RunTheBot/NotAHackPad/pcb/hack_pad.kicad_sch

## KiCad design pcb/hack_pad.kicad_sch (2025-06-08)

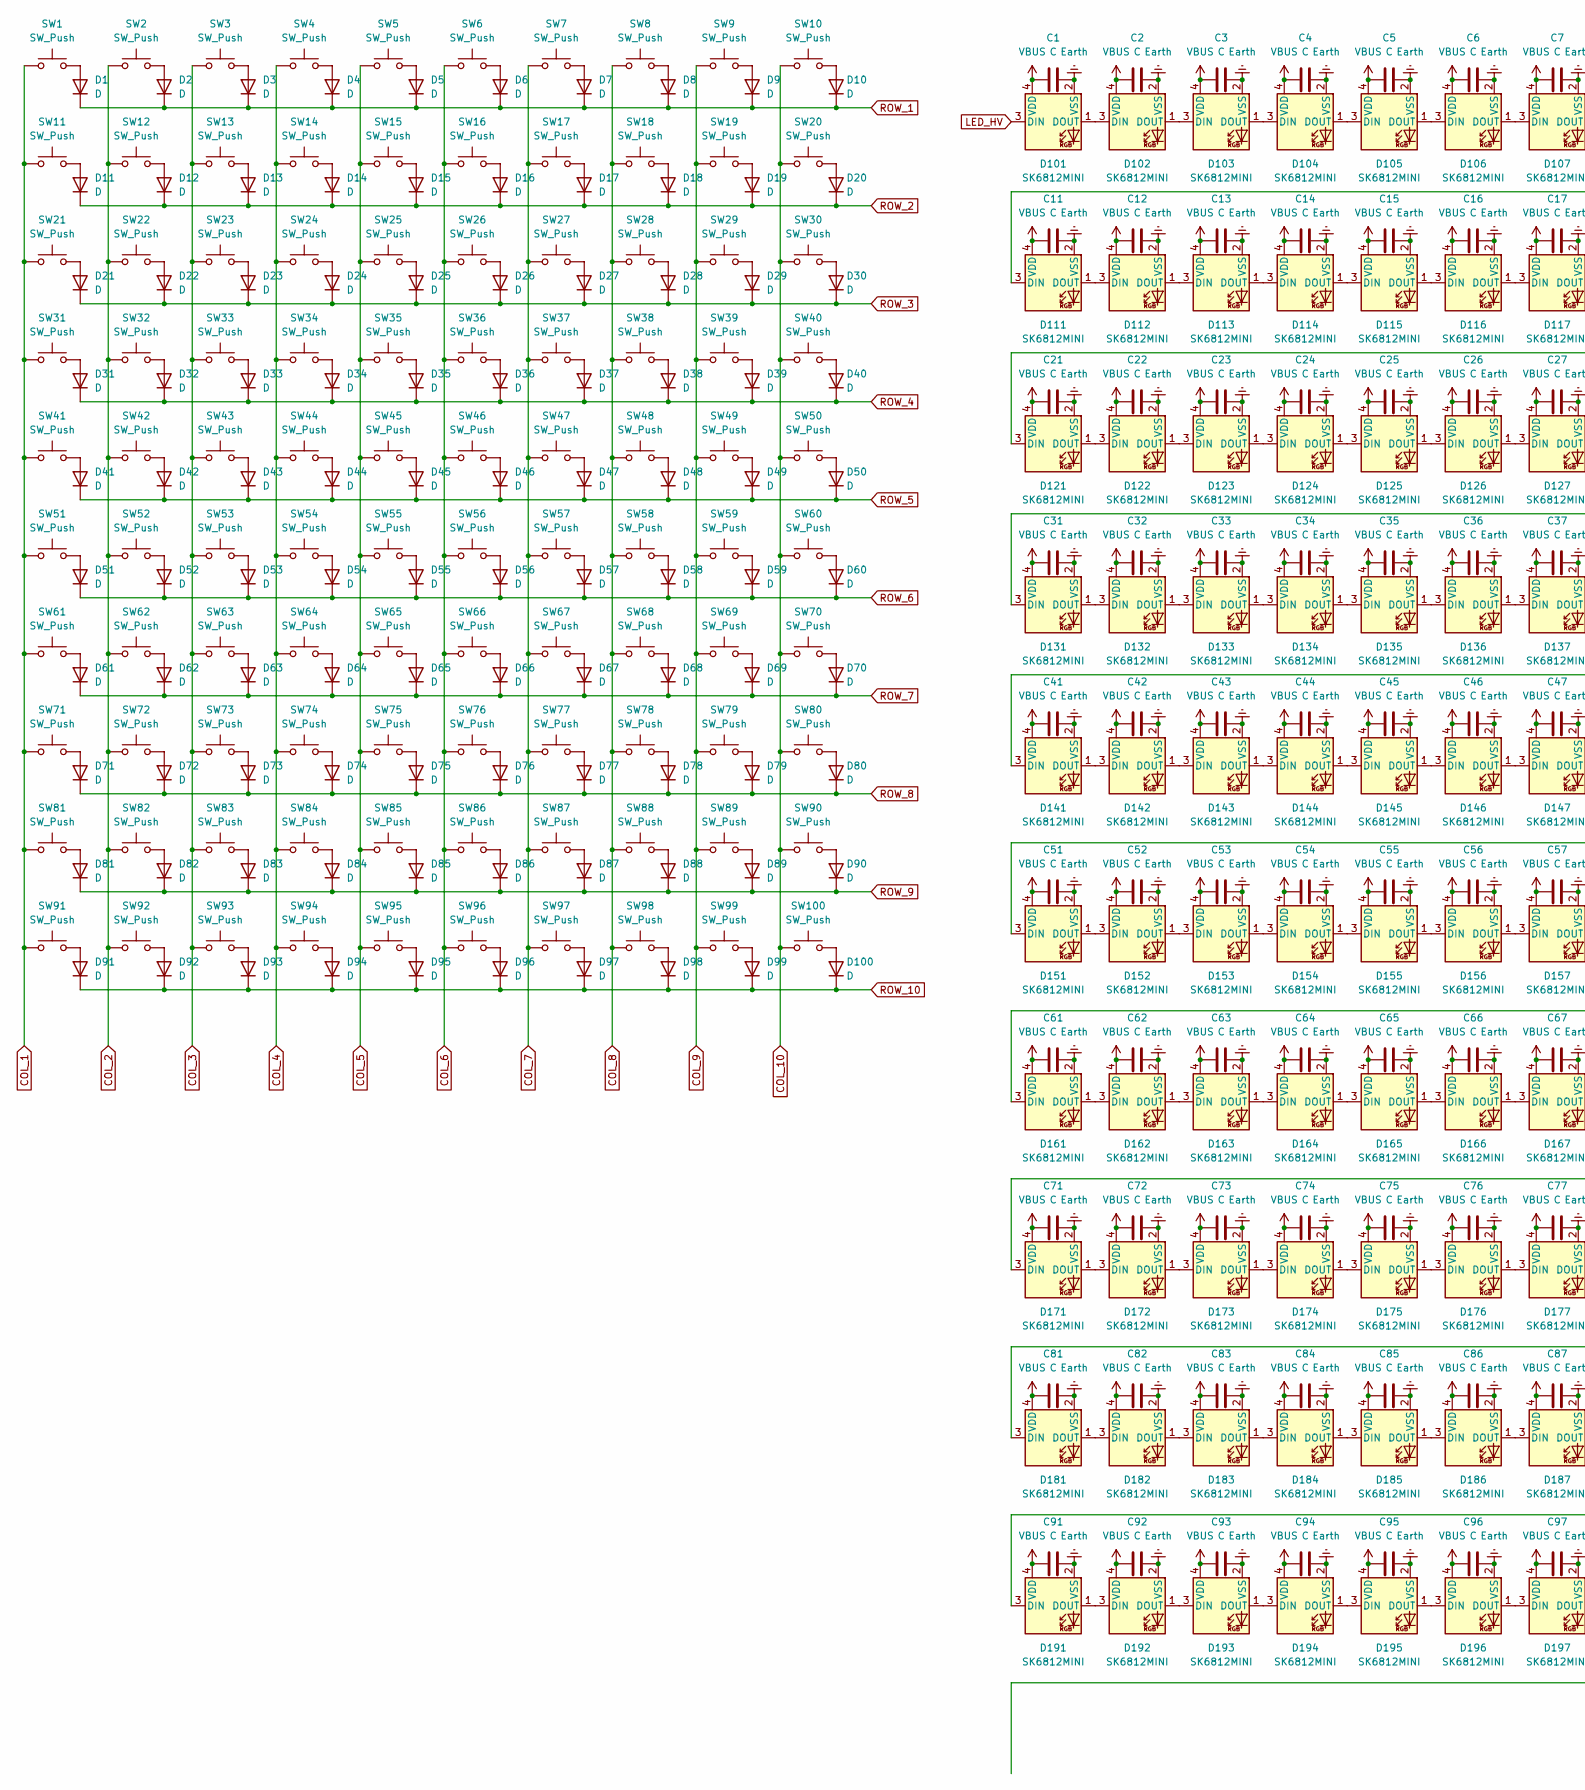
[picture p5: schematic hack_pad.kicad_sch, part in row 1, column 1]

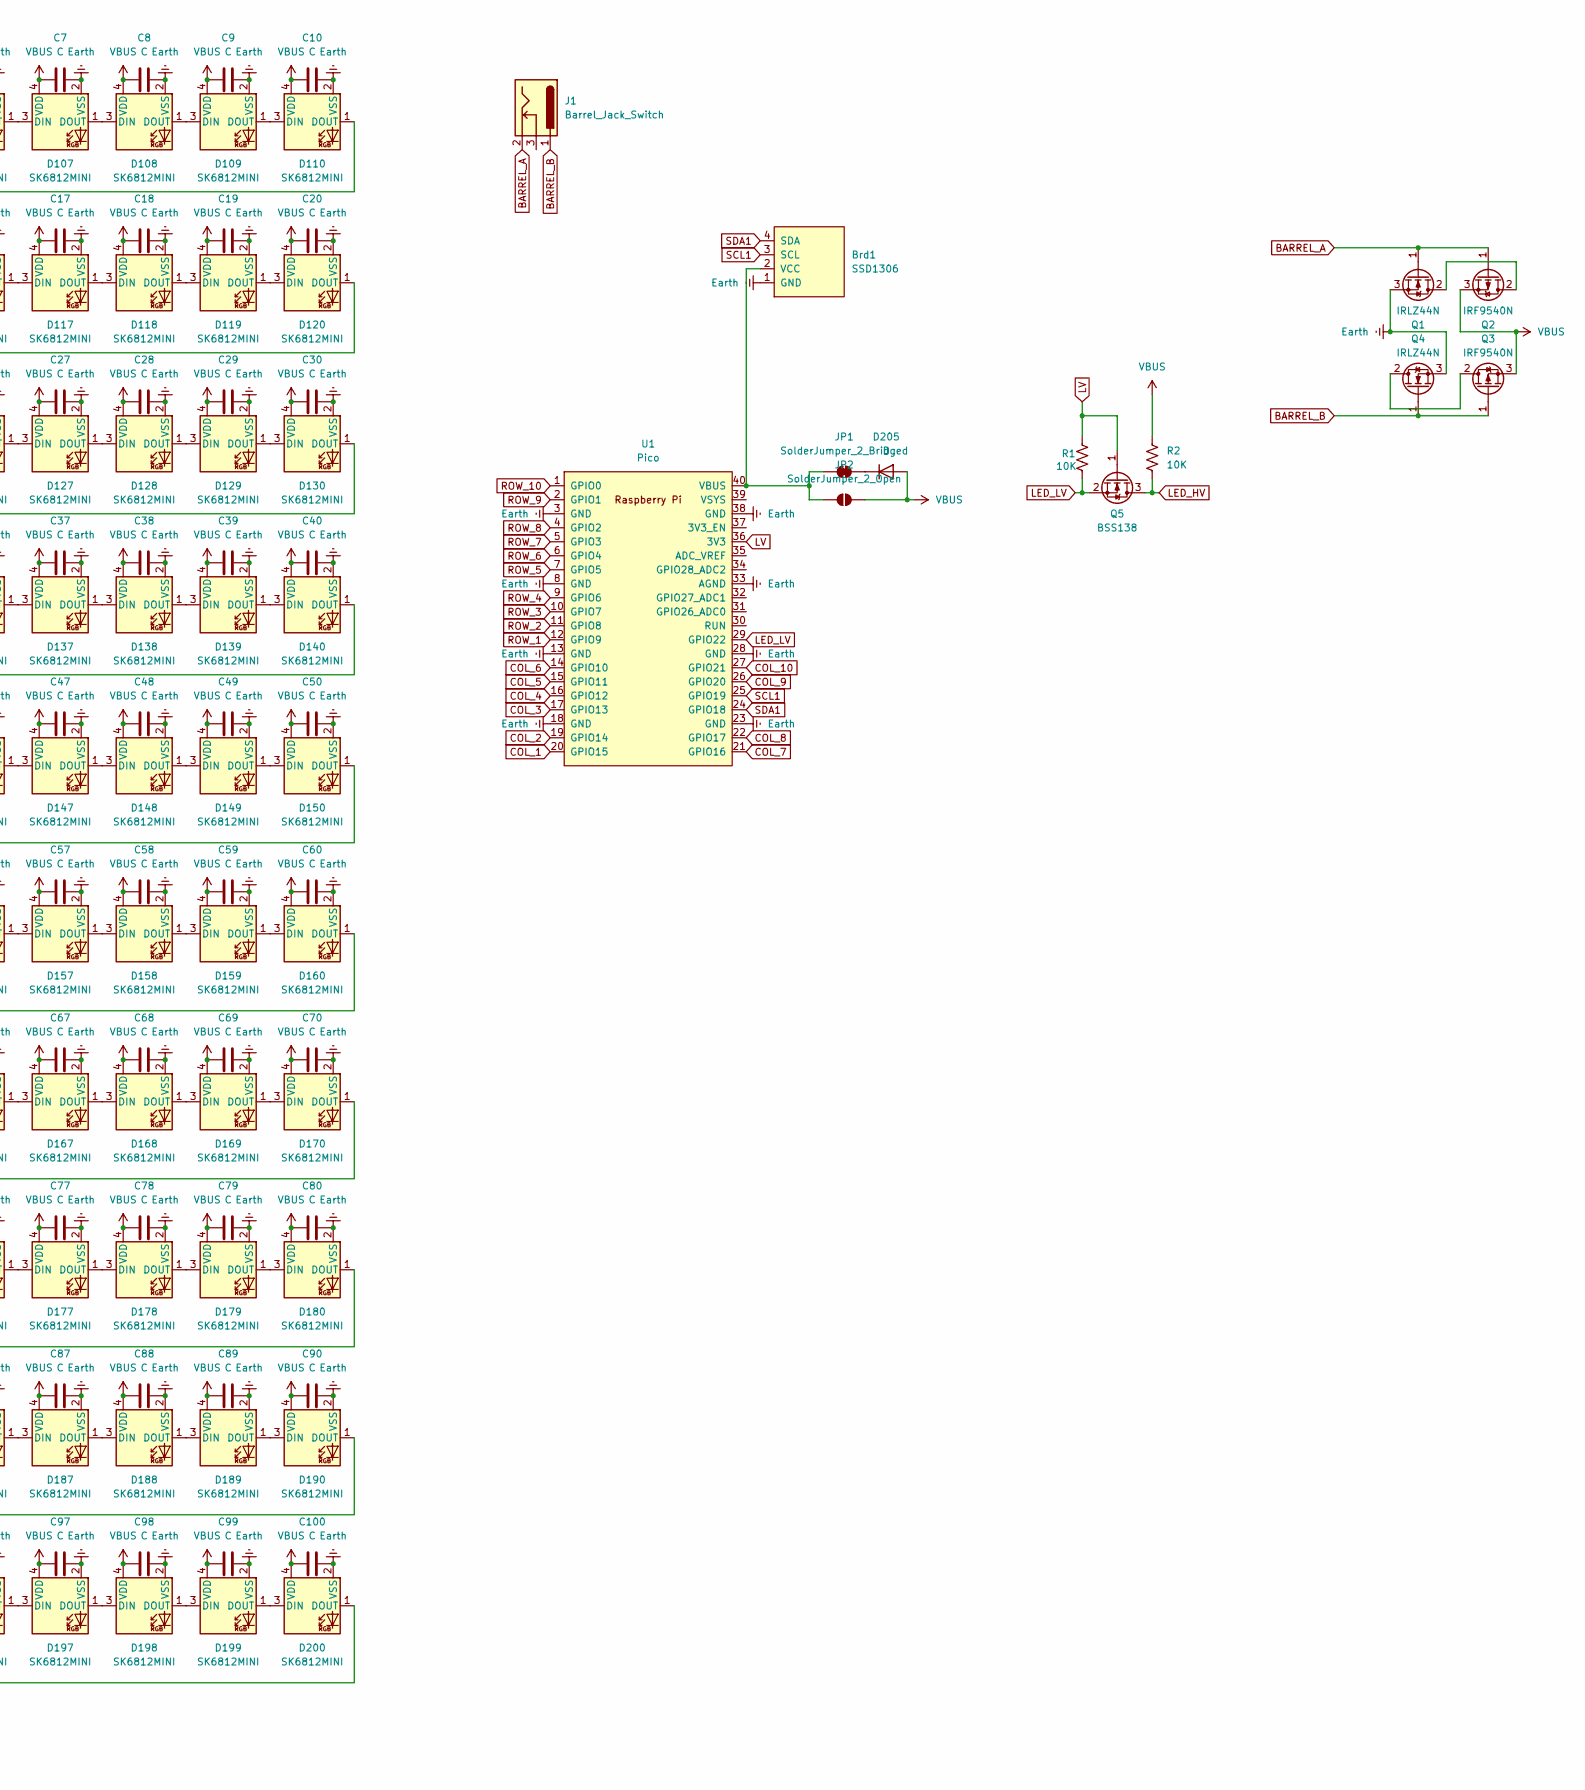
[picture p6: schematic hack_pad.kicad_sch, part in row 1, column 2]

Parts:
Brd1: SSD1306; SSD1306-0.91-OLED-4pin-128x32
C1, C2, C3, C4, C5, C6, C7, C8, C9, C10, C11, C12, C13, C14, C15, C16, C17, C18, C19, C20, C21, C22, C23, C24, C25, C26, C27, C28, C29, C30, C31, C32, C33, C34, C35, C36, C37, C38, C39, C40, C41, C42, C43, C44, C45, C46, C47, C48, C49, C50, C51, C52, C53, C54, C55, C56, C57, C58, C59, C60, C61, C62, C63, C64, C65, C66, C67, C68, C69, C70, C71, C72, C73, C74, C75, C76, C77, C78, C79, C80, C81, C82, C83, C84, C85, C86, C87, C88, C89, C90, C91, C92, C93, C94, C95, C96, C97, C98, C99, C100: C; C_0805_2012Metric_Pad1.18x1.45mm_HandSolder
D1, D2, D3, D4, D5, D6, D7, D8, D9, D10, D11, D12, D13, D14, D15, D16, D17, D18, D19, D20, D21, D22, D23, D24, D25, D26, D27, D28, D29, D30, D31, D32, D33, D34, D35, D36, D37, D38, D39, D40, D41, D42, D43, D44, D45, D46, D47, D48, D49, D50, D51, D52, D53, D54, D55, D56, D57, D58, D59, D60, D61, D62, D63, D64, D65, D66, D67, D68, D69, D70, D71, D72, D73, D74, D75, D76, D77, D78, D79, D80, D81, D82, D83, D84, D85, D86, D87, D88, D89, D90, D91, D92, D93, D94, D95, D96, D97, D98, D99, D100: D; D_SOD-123
D101, D102, D103, D104, D105, D106, D107, D108, D109, D110, D111, D112, D113, D114, D115, D116, D117, D118, D119, D120, D121, D122, D123, D124, D125, D126, D127, D128, D129, D130, D131, D132, D133, D134, D135, D136, D137, D138, D139, D140, D141, D142, D143, D144, D145, D146, D147, D148, D149, D150, D151, D152, D153, D154, D155, D156, D157, D158, D159, D160, D161, D162, D163, D164, D165, D166, D167, D168, D169, D170, D171, D172, D173, D174, D175, D176, D177, D178, D179, D180, D181, D182, D183, D184, D185, D186, D187, D188, D189, D190, D191, D192, D193, D194, D195, D196, D197, D198, D199, D200: SK6812MINI; SK6812MINI-E
D205: D; D_SMA_Handsoldering
J1: Barrel_Jack_Switch; BarrelJack_Horizontal
JP1: SolderJumper_2_Bridged; SolderJumper-2_P1.3mm_Bridged_RoundedPad1.0x1.5mm
JP2: SolderJumper_2_Open; SolderJumper-2_P1.3mm_Open_Pad1.0x1.5mm
Q1, Q4: IRLZ44N; TO-220-3_Horizontal_TabDown
Q2, Q3: IRF9540N; TO-220-3_Horizontal_TabDown
Q5: BSS138; SOT-23
R1, R2: 10K; R_0603_1608Metric_Pad0.98x0.95mm_HandSolder
SW1, SW2, SW3, SW4, SW5, SW6, SW7, SW8, SW9, SW10, SW11, SW12, SW13, SW14, SW15, SW16, SW17, SW18, SW19, SW20, SW21, SW22, SW23, SW24, SW25, SW26, SW27, SW28, SW29, SW30, SW31, SW32, SW33, SW34, SW35, SW36, SW37, SW38, SW39, SW40, SW41, SW42, SW43, SW44, SW45, SW46, SW47, SW48, SW49, SW50, SW51, SW52, SW53, SW54, SW55, SW56, SW57, SW58, SW59, SW60, SW61, SW62, SW63, SW64, SW65, SW66, SW67, SW68, SW69, SW70, SW71, SW72, SW73, SW74, SW75, SW76, SW77, SW78, SW79, SW80, SW81, SW82, SW83, SW84, SW85, SW86, SW87, SW88, SW89, SW90, SW91, SW92, SW93, SW94, SW95, SW96, SW97, SW98, SW99, SW100: SW_Push; SW_Cherry_MX_PCB_1.00u
U1: Pico; RPi_Pico_SMD_TH

Connections:
BARREL_A: J1.2, Q1.1 (G), Q2.1 (G)
BARREL_B: J1.1, Q3.1 (G), Q4.1 (G)
COL_1: SW1.1, SW11.1, SW21.1, SW31.1, SW41.1, SW51.1, SW61.1, SW71.1, SW81.1, SW91.1, U1.20 (GPIO15)
COL_2: SW2.1, SW12.1, SW22.1, SW32.1, SW42.1, SW52.1, SW62.1, SW72.1, SW82.1, SW92.1, U1.19 (GPIO14)
COL_3: SW3.1, SW13.1, SW23.1, SW33.1, SW43.1, SW53.1, SW63.1, SW73.1, SW83.1, SW93.1, U1.17 (GPIO13)
COL_4: SW4.1, SW14.1, SW24.1, SW34.1, SW44.1, SW54.1, SW64.1, SW74.1, SW84.1, SW94.1, U1.16 (GPIO12)
COL_5: SW5.1, SW15.1, SW25.1, SW35.1, SW45.1, SW55.1, SW65.1, SW75.1, SW85.1, SW95.1, U1.15 (GPIO11)
COL_6: SW6.1, SW16.1, SW26.1, SW36.1, SW46.1, SW56.1, SW66.1, SW76.1, SW86.1, SW96.1, U1.14 (GPIO10)
COL_7: SW7.1, SW17.1, SW27.1, SW37.1, SW47.1, SW57.1, SW67.1, SW77.1, SW87.1, SW97.1, U1.21 (GPIO16)
COL_8: SW8.1, SW18.1, SW28.1, SW38.1, SW48.1, SW58.1, SW68.1, SW78.1, SW88.1, SW98.1, U1.22 (GPIO17)
COL_9: SW9.1, SW19.1, SW29.1, SW39.1, SW49.1, SW59.1, SW69.1, SW79.1, SW89.1, SW99.1, U1.26 (GPIO20)
COL_10: SW10.1, SW20.1, SW30.1, SW40.1, SW50.1, SW60.1, SW70.1, SW80.1, SW90.1, SW100.1, U1.27 (GPIO21)
Earth: Brd1.1 (GND), C1.2, C2.2, C3.2, C4.2, C5.2, C6.2, C7.2, C8.2, C9.2, C10.2, C11.2, C12.2, C13.2, C14.2, C15.2, C16.2, C17.2, C18.2, C19.2, C20.2, C21.2, C22.2, C23.2, C24.2, C25.2, C26.2, C27.2, C28.2, C29.2, C30.2, C31.2, C32.2, C33.2, C34.2, C35.2, C36.2, C37.2, C38.2, C39.2, C40.2, C41.2, C42.2, C43.2, C44.2, C45.2, C46.2, C47.2, C48.2, C49.2, C50.2, C51.2, C52.2, C53.2, C54.2, C55.2, C56.2, C57.2, C58.2, C59.2, C60.2, C61.2, C62.2, C63.2, C64.2, C65.2, C66.2, C67.2, C68.2, C69.2, C70.2, C71.2, C72.2, C73.2, C74.2, C75.2, C76.2, C77.2, C78.2, C79.2, C80.2, C81.2, C82.2, C83.2, C84.2, C85.2, C86.2, C87.2, C88.2, C89.2, C90.2, C91.2, C92.2, C93.2, C94.2, C95.2, C96.2, C97.2, C98.2, C99.2, C100.2, D101.2 (VSS), D102.2 (VSS), D103.2 (VSS), D104.2 (VSS), D105.2 (VSS), D106.2 (VSS), D107.2 (VSS), D108.2 (VSS), D109.2 (VSS), D110.2 (VSS), D111.2 (VSS), D112.2 (VSS), D113.2 (VSS), D114.2 (VSS), D115.2 (VSS), D116.2 (VSS), D117.2 (VSS), D118.2 (VSS), D119.2 (VSS), D120.2 (VSS), D121.2 (VSS), D122.2 (VSS), D123.2 (VSS), D124.2 (VSS), D125.2 (VSS), D126.2 (VSS), D127.2 (VSS), D128.2 (VSS), D129.2 (VSS), D130.2 (VSS), D131.2 (VSS), D132.2 (VSS), D133.2 (VSS), D134.2 (VSS), D135.2 (VSS), D136.2 (VSS), D137.2 (VSS), D138.2 (VSS), D139.2 (VSS), D140.2 (VSS), D141.2 (VSS), D142.2 (VSS), D143.2 (VSS), D144.2 (VSS), D145.2 (VSS), D146.2 (VSS), D147.2 (VSS), D148.2 (VSS), D149.2 (VSS), D150.2 (VSS), D151.2 (VSS), D152.2 (VSS), D153.2 (VSS), D154.2 (VSS), D155.2 (VSS), D156.2 (VSS), D157.2 (VSS), D158.2 (VSS), D159.2 (VSS), D160.2 (VSS), D161.2 (VSS), D162.2 (VSS), D163.2 (VSS), D164.2 (VSS), D165.2 (VSS), D166.2 (VSS), D167.2 (VSS), D168.2 (VSS), D169.2 (VSS), D170.2 (VSS), D171.2 (VSS), D172.2 (VSS), D173.2 (VSS), D174.2 (VSS), D175.2 (VSS), D176.2 (VSS), D177.2 (VSS), D178.2 (VSS), D179.2 (VSS), D180.2 (VSS), D181.2 (VSS), D182.2 (VSS), D183.2 (VSS), D184.2 (VSS), D185.2 (VSS), D186.2 (VSS), D187.2 (VSS), D188.2 (VSS), D189.2 (VSS), D190.2 (VSS), D191.2 (VSS), D192.2 (VSS), D193.2 (VSS), D194.2 (VSS), D195.2 (VSS), D196.2 (VSS), D197.2 (VSS), D198.2 (VSS), D199.2 (VSS), D200.2 (VSS), Q1.3 (S), Q4.3 (S), U1.3 (GND), U1.8 (GND), U1.13 (GND), U1.18 (GND), U1.23 (GND), U1.28 (GND), U1.33 (AGND), U1.38 (GND)
LED_HV: D101.3 (DIN), Q5.3 (D), R2.2
LED_LV: Q5.2 (S), R1.2, U1.29 (GPIO22)
LV: Q5.1 (G), R1.1, U1.36 (3V3)
unnamed: Brd1.2 (VCC), JP1.1 (A), JP2.1 (A), U1.40 (VBUS)
unnamed: D1.2 (A), SW1.2
unnamed: D2.2 (A), SW2.2
unnamed: D3.2 (A), SW3.2
unnamed: D4.2 (A), SW4.2
unnamed: D5.2 (A), SW5.2
unnamed: D6.2 (A), SW6.2
unnamed: D7.2 (A), SW7.2
unnamed: D8.2 (A), SW8.2
unnamed: D9.2 (A), SW9.2
unnamed: D10.2 (A), SW10.2
unnamed: D11.2 (A), SW11.2
unnamed: D12.2 (A), SW12.2
unnamed: D13.2 (A), SW13.2
unnamed: D14.2 (A), SW14.2
unnamed: D15.2 (A), SW15.2
unnamed: D16.2 (A), SW16.2
unnamed: D17.2 (A), SW17.2
unnamed: D18.2 (A), SW18.2
unnamed: D19.2 (A), SW19.2
unnamed: D20.2 (A), SW20.2
unnamed: D21.2 (A), SW21.2
unnamed: D22.2 (A), SW22.2
unnamed: D23.2 (A), SW23.2
unnamed: D24.2 (A), SW24.2
unnamed: D25.2 (A), SW25.2
unnamed: D26.2 (A), SW26.2
unnamed: D27.2 (A), SW27.2
unnamed: D28.2 (A), SW28.2
unnamed: D29.2 (A), SW29.2
unnamed: D30.2 (A), SW30.2
unnamed: D31.2 (A), SW31.2
unnamed: D32.2 (A), SW32.2
unnamed: D33.2 (A), SW33.2
unnamed: D34.2 (A), SW34.2
unnamed: D35.2 (A), SW35.2
unnamed: D36.2 (A), SW36.2
unnamed: D37.2 (A), SW37.2
unnamed: D38.2 (A), SW38.2
unnamed: D39.2 (A), SW39.2
unnamed: D40.2 (A), SW40.2
unnamed: D41.2 (A), SW41.2
unnamed: D42.2 (A), SW42.2
unnamed: D43.2 (A), SW43.2
unnamed: D44.2 (A), SW44.2
unnamed: D45.2 (A), SW45.2
unnamed: D46.2 (A), SW46.2
unnamed: D47.2 (A), SW47.2
unnamed: D48.2 (A), SW48.2
unnamed: D49.2 (A), SW49.2
unnamed: D50.2 (A), SW50.2
unnamed: D51.2 (A), SW51.2
unnamed: D52.2 (A), SW52.2
unnamed: D53.2 (A), SW53.2
unnamed: D54.2 (A), SW54.2
unnamed: D55.2 (A), SW55.2
unnamed: D56.2 (A), SW56.2
unnamed: D57.2 (A), SW57.2
unnamed: D58.2 (A), SW58.2
unnamed: D59.2 (A), SW59.2
unnamed: D60.2 (A), SW60.2
unnamed: D61.2 (A), SW61.2
unnamed: D62.2 (A), SW62.2
unnamed: D63.2 (A), SW63.2
unnamed: D64.2 (A), SW64.2
unnamed: D65.2 (A), SW65.2
unnamed: D66.2 (A), SW66.2
unnamed: D67.2 (A), SW67.2
unnamed: D68.2 (A), SW68.2
unnamed: D69.2 (A), SW69.2
unnamed: D70.2 (A), SW70.2
unnamed: D71.2 (A), SW71.2
unnamed: D72.2 (A), SW72.2
unnamed: D73.2 (A), SW73.2
unnamed: D74.2 (A), SW74.2
unnamed: D75.2 (A), SW75.2
unnamed: D76.2 (A), SW76.2
unnamed: D77.2 (A), SW77.2
unnamed: D78.2 (A), SW78.2
unnamed: D79.2 (A), SW79.2
unnamed: D80.2 (A), SW80.2
unnamed: D81.2 (A), SW81.2
unnamed: D82.2 (A), SW82.2
unnamed: D83.2 (A), SW83.2
unnamed: D84.2 (A), SW84.2
unnamed: D85.2 (A), SW85.2
unnamed: D86.2 (A), SW86.2
unnamed: D87.2 (A), SW87.2
unnamed: D88.2 (A), SW88.2
unnamed: D89.2 (A), SW89.2
unnamed: D90.2 (A), SW90.2
unnamed: D91.2 (A), SW91.2
unnamed: D92.2 (A), SW92.2
unnamed: D93.2 (A), SW93.2
unnamed: D94.2 (A), SW94.2
unnamed: D95.2 (A), SW95.2
unnamed: D96.2 (A), SW96.2
unnamed: D97.2 (A), SW97.2
unnamed: D98.2 (A), SW98.2
unnamed: D99.2 (A), SW99.2
unnamed: D100.2 (A), SW100.2
unnamed: D101.1 (DOUT), D102.3 (DIN)
unnamed: D102.1 (DOUT), D103.3 (DIN)
unnamed: D103.1 (DOUT), D104.3 (DIN)
unnamed: D104.1 (DOUT), D105.3 (DIN)
unnamed: D105.1 (DOUT), D106.3 (DIN)
unnamed: D106.1 (DOUT), D107.3 (DIN)
unnamed: D107.1 (DOUT), D108.3 (DIN)
unnamed: D108.1 (DOUT), D109.3 (DIN)
unnamed: D109.1 (DOUT), D110.3 (DIN)
unnamed: D110.1 (DOUT), D111.3 (DIN)
unnamed: D111.1 (DOUT), D112.3 (DIN)
unnamed: D112.1 (DOUT), D113.3 (DIN)
unnamed: D113.1 (DOUT), D114.3 (DIN)
unnamed: D114.1 (DOUT), D115.3 (DIN)
unnamed: D115.1 (DOUT), D116.3 (DIN)
unnamed: D116.1 (DOUT), D117.3 (DIN)
unnamed: D117.1 (DOUT), D118.3 (DIN)
unnamed: D118.1 (DOUT), D119.3 (DIN)
unnamed: D119.1 (DOUT), D120.3 (DIN)
unnamed: D120.1 (DOUT), D121.3 (DIN)
unnamed: D121.1 (DOUT), D122.3 (DIN)
unnamed: D122.1 (DOUT), D123.3 (DIN)
unnamed: D123.1 (DOUT), D124.3 (DIN)
unnamed: D124.1 (DOUT), D125.3 (DIN)
unnamed: D125.1 (DOUT), D126.3 (DIN)
unnamed: D126.1 (DOUT), D127.3 (DIN)
unnamed: D127.1 (DOUT), D128.3 (DIN)
unnamed: D128.1 (DOUT), D129.3 (DIN)
unnamed: D129.1 (DOUT), D130.3 (DIN)
unnamed: D130.1 (DOUT), D131.3 (DIN)
unnamed: D131.1 (DOUT), D132.3 (DIN)
unnamed: D132.1 (DOUT), D133.3 (DIN)
unnamed: D133.1 (DOUT), D134.3 (DIN)
unnamed: D134.1 (DOUT), D135.3 (DIN)
unnamed: D135.1 (DOUT), D136.3 (DIN)
unnamed: D136.1 (DOUT), D137.3 (DIN)
unnamed: D137.1 (DOUT), D138.3 (DIN)
unnamed: D138.1 (DOUT), D139.3 (DIN)
unnamed: D139.1 (DOUT), D140.3 (DIN)
unnamed: D140.1 (DOUT), D141.3 (DIN)
unnamed: D141.1 (DOUT), D142.3 (DIN)
unnamed: D142.1 (DOUT), D143.3 (DIN)
unnamed: D143.1 (DOUT), D144.3 (DIN)
unnamed: D144.1 (DOUT), D145.3 (DIN)
unnamed: D145.1 (DOUT), D146.3 (DIN)
unnamed: D146.1 (DOUT), D147.3 (DIN)
unnamed: D147.1 (DOUT), D148.3 (DIN)
unnamed: D148.1 (DOUT), D149.3 (DIN)
unnamed: D149.1 (DOUT), D150.3 (DIN)
unnamed: D150.1 (DOUT), D151.3 (DIN)
unnamed: D151.1 (DOUT), D152.3 (DIN)
unnamed: D152.1 (DOUT), D153.3 (DIN)
unnamed: D153.1 (DOUT), D154.3 (DIN)
unnamed: D154.1 (DOUT), D155.3 (DIN)
unnamed: D155.1 (DOUT), D156.3 (DIN)
unnamed: D156.1 (DOUT), D157.3 (DIN)
unnamed: D157.1 (DOUT), D158.3 (DIN)
unnamed: D158.1 (DOUT), D159.3 (DIN)
unnamed: D159.1 (DOUT), D160.3 (DIN)
unnamed: D160.1 (DOUT), D161.3 (DIN)
unnamed: D161.1 (DOUT), D162.3 (DIN)
unnamed: D162.1 (DOUT), D163.3 (DIN)
unnamed: D163.1 (DOUT), D164.3 (DIN)
unnamed: D164.1 (DOUT), D165.3 (DIN)
unnamed: D165.1 (DOUT), D166.3 (DIN)
unnamed: D166.1 (DOUT), D167.3 (DIN)
unnamed: D167.1 (DOUT), D168.3 (DIN)
unnamed: D168.1 (DOUT), D169.3 (DIN)
unnamed: D169.1 (DOUT), D170.3 (DIN)
unnamed: D170.1 (DOUT), D171.3 (DIN)
unnamed: D171.1 (DOUT), D172.3 (DIN)
unnamed: D172.1 (DOUT), D173.3 (DIN)
unnamed: D173.1 (DOUT), D174.3 (DIN)
unnamed: D174.1 (DOUT), D175.3 (DIN)
unnamed: D175.1 (DOUT), D176.3 (DIN)
unnamed: D176.1 (DOUT), D177.3 (DIN)
unnamed: D177.1 (DOUT), D178.3 (DIN)
unnamed: D178.1 (DOUT), D179.3 (DIN)
unnamed: D179.1 (DOUT), D180.3 (DIN)
unnamed: D180.1 (DOUT), D181.3 (DIN)
unnamed: D181.1 (DOUT), D182.3 (DIN)
unnamed: D182.1 (DOUT), D183.3 (DIN)
unnamed: D183.1 (DOUT), D184.3 (DIN)
unnamed: D184.1 (DOUT), D185.3 (DIN)
unnamed: D185.1 (DOUT), D186.3 (DIN)
unnamed: D186.1 (DOUT), D187.3 (DIN)
unnamed: D187.1 (DOUT), D188.3 (DIN)
unnamed: D188.1 (DOUT), D189.3 (DIN)
unnamed: D189.1 (DOUT), D190.3 (DIN)
unnamed: D190.1 (DOUT), D191.3 (DIN)
unnamed: D191.1 (DOUT), D192.3 (DIN)
unnamed: D192.1 (DOUT), D193.3 (DIN)
unnamed: D193.1 (DOUT), D194.3 (DIN)
unnamed: D194.1 (DOUT), D195.3 (DIN)
unnamed: D195.1 (DOUT), D196.3 (DIN)
unnamed: D196.1 (DOUT), D197.3 (DIN)
unnamed: D197.1 (DOUT), D198.3 (DIN)
unnamed: D198.1 (DOUT), D199.3 (DIN)
unnamed: D199.1 (DOUT), D200.3 (DIN)
unnamed: D205.1 (K), JP1.2 (B)
unnamed: Q1.2 (D), Q2.2 (D)
unnamed: Q3.2 (D), Q4.2 (D)
ROW_1: D1.1 (K), D2.1 (K), D3.1 (K), D4.1 (K), D5.1 (K), D6.1 (K), D7.1 (K), D8.1 (K), D9.1 (K), D10.1 (K), U1.12 (GPIO9)
ROW_2: D11.1 (K), D12.1 (K), D13.1 (K), D14.1 (K), D15.1 (K), D16.1 (K), D17.1 (K), D18.1 (K), D19.1 (K), D20.1 (K), U1.11 (GPIO8)
ROW_3: D21.1 (K), D22.1 (K), D23.1 (K), D24.1 (K), D25.1 (K), D26.1 (K), D27.1 (K), D28.1 (K), D29.1 (K), D30.1 (K), U1.10 (GPIO7)
ROW_4: D31.1 (K), D32.1 (K), D33.1 (K), D34.1 (K), D35.1 (K), D36.1 (K), D37.1 (K), D38.1 (K), D39.1 (K), D40.1 (K), U1.9 (GPIO6)
ROW_5: D41.1 (K), D42.1 (K), D43.1 (K), D44.1 (K), D45.1 (K), D46.1 (K), D47.1 (K), D48.1 (K), D49.1 (K), D50.1 (K), U1.7 (GPIO5)
ROW_6: D51.1 (K), D52.1 (K), D53.1 (K), D54.1 (K), D55.1 (K), D56.1 (K), D57.1 (K), D58.1 (K), D59.1 (K), D60.1 (K), U1.6 (GPIO4)
ROW_7: D61.1 (K), D62.1 (K), D63.1 (K), D64.1 (K), D65.1 (K), D66.1 (K), D67.1 (K), D68.1 (K), D69.1 (K), D70.1 (K), U1.5 (GPIO3)
ROW_8: D71.1 (K), D72.1 (K), D73.1 (K), D74.1 (K), D75.1 (K), D76.1 (K), D77.1 (K), D78.1 (K), D79.1 (K), D80.1 (K), U1.4 (GPIO2)
ROW_9: D81.1 (K), D82.1 (K), D83.1 (K), D84.1 (K), D85.1 (K), D86.1 (K), D87.1 (K), D88.1 (K), D89.1 (K), D90.1 (K), U1.2 (GPIO1)
ROW_10: D91.1 (K), D92.1 (K), D93.1 (K), D94.1 (K), D95.1 (K), D96.1 (K), D97.1 (K), D98.1 (K), D99.1 (K), D100.1 (K), U1.1 (GPIO0)
SCL1: Brd1.3 (SCL), U1.25 (GPIO19)
SDA1: Brd1.4 (SDA), U1.24 (GPIO18)
VBUS: C1.1, C2.1, C3.1, C4.1, C5.1, C6.1, C7.1, C8.1, C9.1, C10.1, C11.1, C12.1, C13.1, C14.1, C15.1, C16.1, C17.1, C18.1, C19.1, C20.1, C21.1, C22.1, C23.1, C24.1, C25.1, C26.1, C27.1, C28.1, C29.1, C30.1, C31.1, C32.1, C33.1, C34.1, C35.1, C36.1, C37.1, C38.1, C39.1, C40.1, C41.1, C42.1, C43.1, C44.1, C45.1, C46.1, C47.1, C48.1, C49.1, C50.1, C51.1, C52.1, C53.1, C54.1, C55.1, C56.1, C57.1, C58.1, C59.1, C60.1, C61.1, C62.1, C63.1, C64.1, C65.1, C66.1, C67.1, C68.1, C69.1, C70.1, C71.1, C72.1, C73.1, C74.1, C75.1, C76.1, C77.1, C78.1, C79.1, C80.1, C81.1, C82.1, C83.1, C84.1, C85.1, C86.1, C87.1, C88.1, C89.1, C90.1, C91.1, C92.1, C93.1, C94.1, C95.1, C96.1, C97.1, C98.1, C99.1, C100.1, D101.4 (VDD), D102.4 (VDD), D103.4 (VDD), D104.4 (VDD), D105.4 (VDD), D106.4 (VDD), D107.4 (VDD), D108.4 (VDD), D109.4 (VDD), D110.4 (VDD), D111.4 (VDD), D112.4 (VDD), D113.4 (VDD), D114.4 (VDD), D115.4 (VDD), D116.4 (VDD), D117.4 (VDD), D118.4 (VDD), D119.4 (VDD), D120.4 (VDD), D121.4 (VDD), D122.4 (VDD), D123.4 (VDD), D124.4 (VDD), D125.4 (VDD), D126.4 (VDD), D127.4 (VDD), D128.4 (VDD), D129.4 (VDD), D130.4 (VDD), D131.4 (VDD), D132.4 (VDD), D133.4 (VDD), D134.4 (VDD), D135.4 (VDD), D136.4 (VDD), D137.4 (VDD), D138.4 (VDD), D139.4 (VDD), D140.4 (VDD), D141.4 (VDD), D142.4 (VDD), D143.4 (VDD), D144.4 (VDD), D145.4 (VDD), D146.4 (VDD), D147.4 (VDD), D148.4 (VDD), D149.4 (VDD), D150.4 (VDD), D151.4 (VDD), D152.4 (VDD), D153.4 (VDD), D154.4 (VDD), D155.4 (VDD), D156.4 (VDD), D157.4 (VDD), D158.4 (VDD), D159.4 (VDD), D160.4 (VDD), D161.4 (VDD), D162.4 (VDD), D163.4 (VDD), D164.4 (VDD), D165.4 (VDD), D166.4 (VDD), D167.4 (VDD), D168.4 (VDD), D169.4 (VDD), D170.4 (VDD), D171.4 (VDD), D172.4 (VDD), D173.4 (VDD), D174.4 (VDD), D175.4 (VDD), D176.4 (VDD), D177.4 (VDD), D178.4 (VDD), D179.4 (VDD), D180.4 (VDD), D181.4 (VDD), D182.4 (VDD), D183.4 (VDD), D184.4 (VDD), D185.4 (VDD), D186.4 (VDD), D187.4 (VDD), D188.4 (VDD), D189.4 (VDD), D190.4 (VDD), D191.4 (VDD), D192.4 (VDD), D193.4 (VDD), D194.4 (VDD), D195.4 (VDD), D196.4 (VDD), D197.4 (VDD), D198.4 (VDD), D199.4 (VDD), D200.4 (VDD), D205.2 (A), JP2.2 (B), Q2.3 (S), Q3.3 (S), R2.1
